Makerspace-Amiens/2024-VRFlightSimulator/docs/images/manettes_de_gaz.jpg

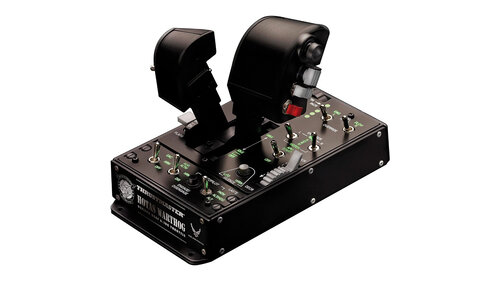
docs/images/manettes_de_gaz.jpg
